wisdom-km/color-eink-work-badge/hardware/portrait/enclosure/output/portrait_native_C1_front.png

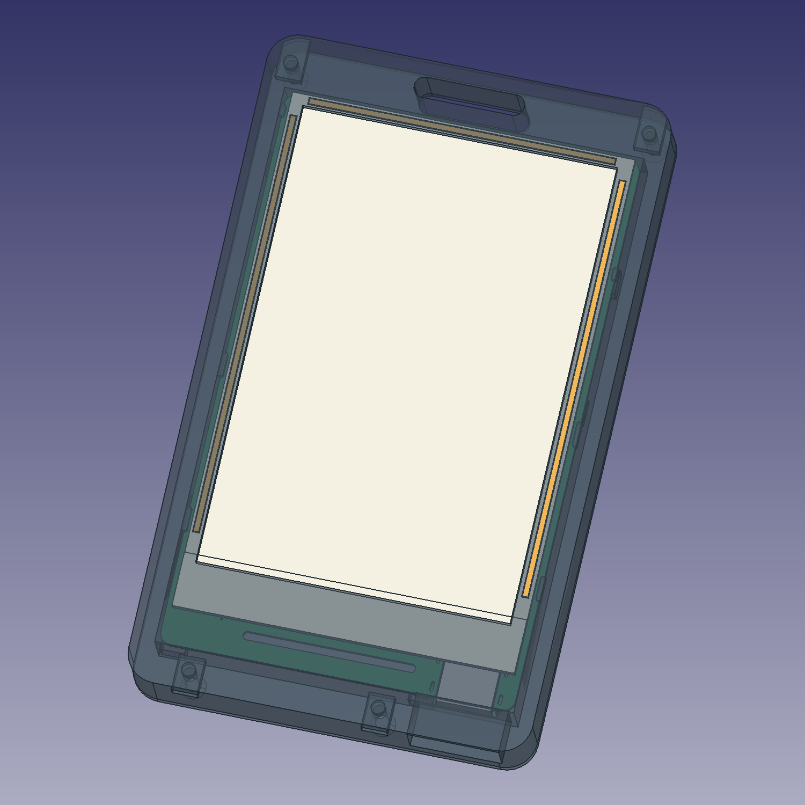
hardware/portrait/enclosure/output/portrait_native_C1_front.png
