wisdom-km/color-eink-work-badge/hardware/portrait/enclosure/output/pcb_back_layout_clipped.png

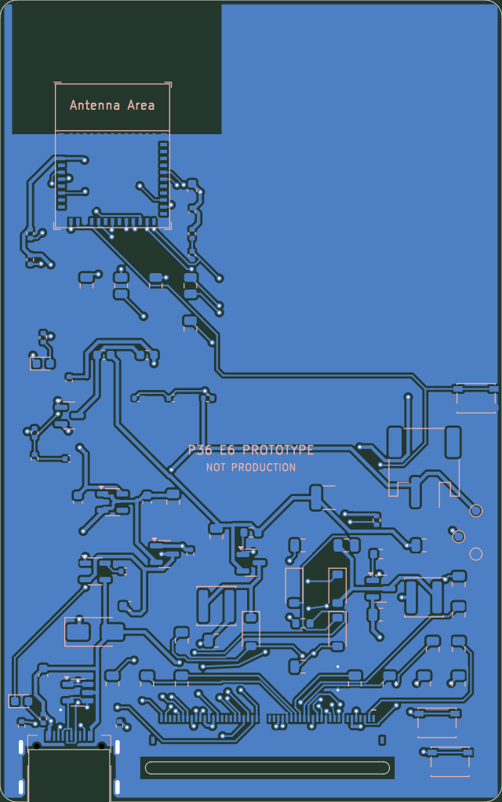
hardware/portrait/enclosure/output/pcb_back_layout_clipped.png
