wisdom-km/color-eink-work-badge/hardware/portrait/enclosure/output/portrait_actual_section.png

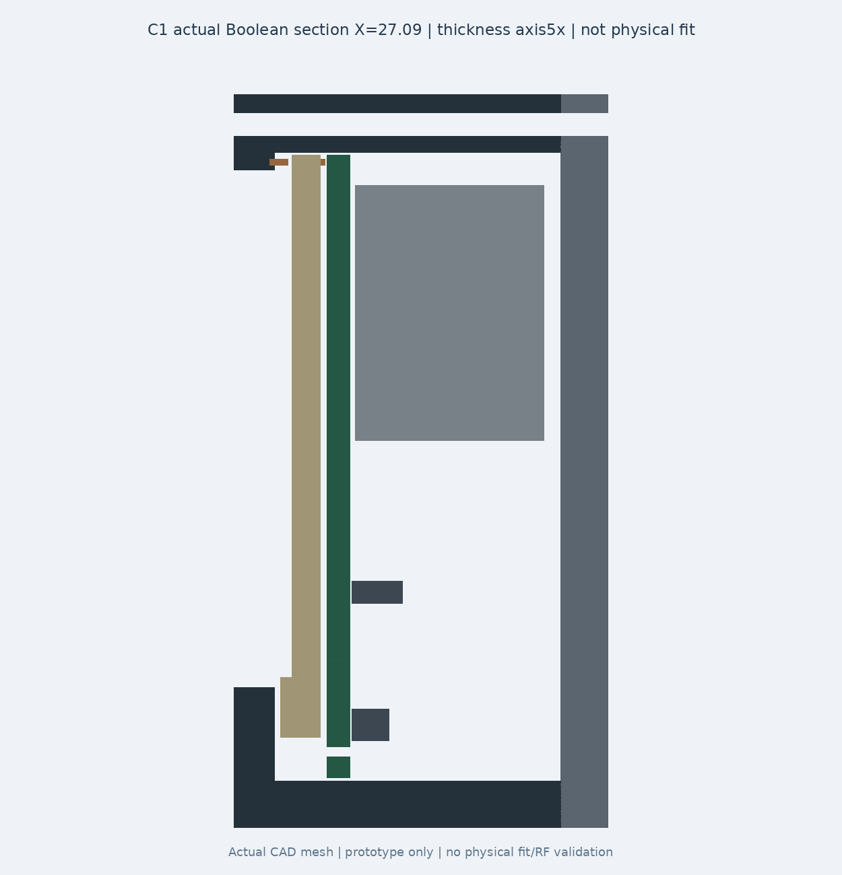
hardware/portrait/enclosure/output/portrait_actual_section.png
