wisdom-km/color-eink-work-badge/hardware/portrait/enclosure/output/portrait_exploded.png

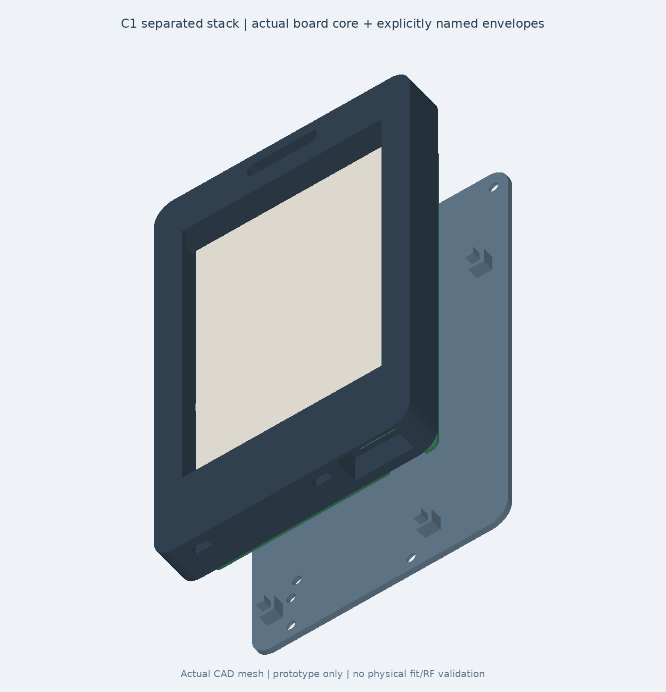
hardware/portrait/enclosure/output/portrait_exploded.png
