wisdom-km/color-eink-work-badge/hardware/portrait/enclosure/output/portrait_internal_envelopes.png

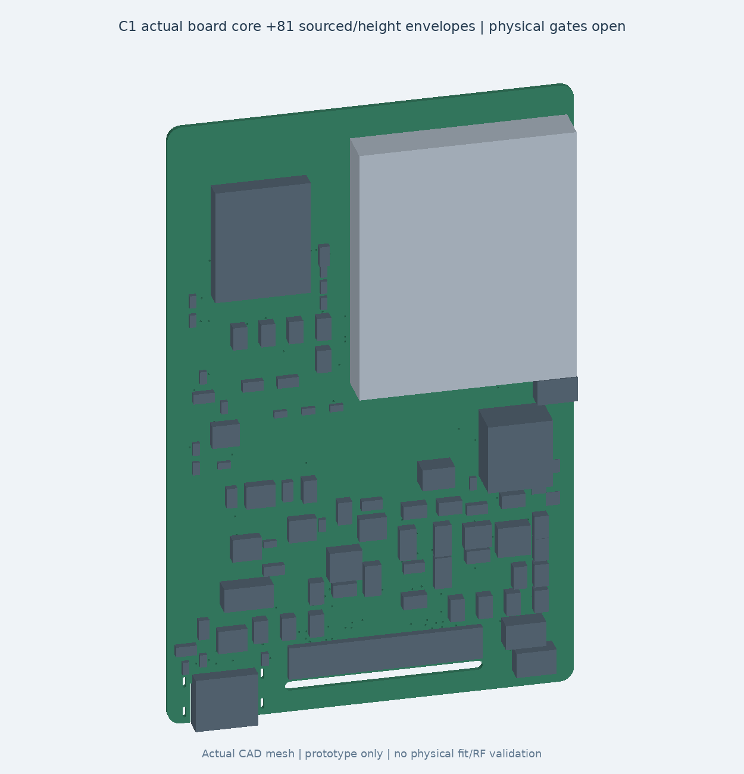
hardware/portrait/enclosure/output/portrait_internal_envelopes.png
