wisdom-km/color-eink-work-badge/hardware/portrait/enclosure/output/portrait_iso_front.png

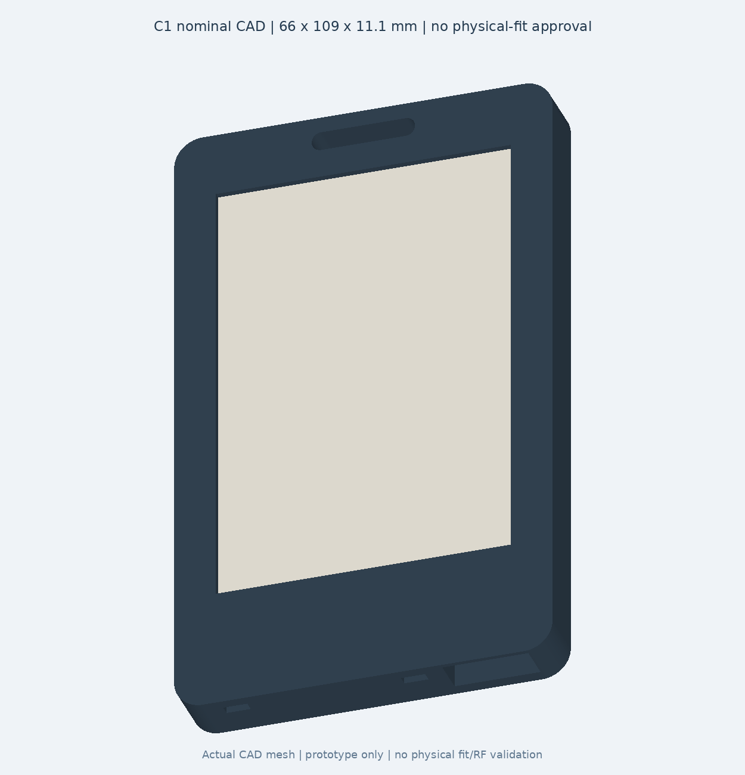
hardware/portrait/enclosure/output/portrait_iso_front.png
