wisdom-km/color-eink-work-badge/hardware/portrait/enclosure/output/portrait_layer_stack.png

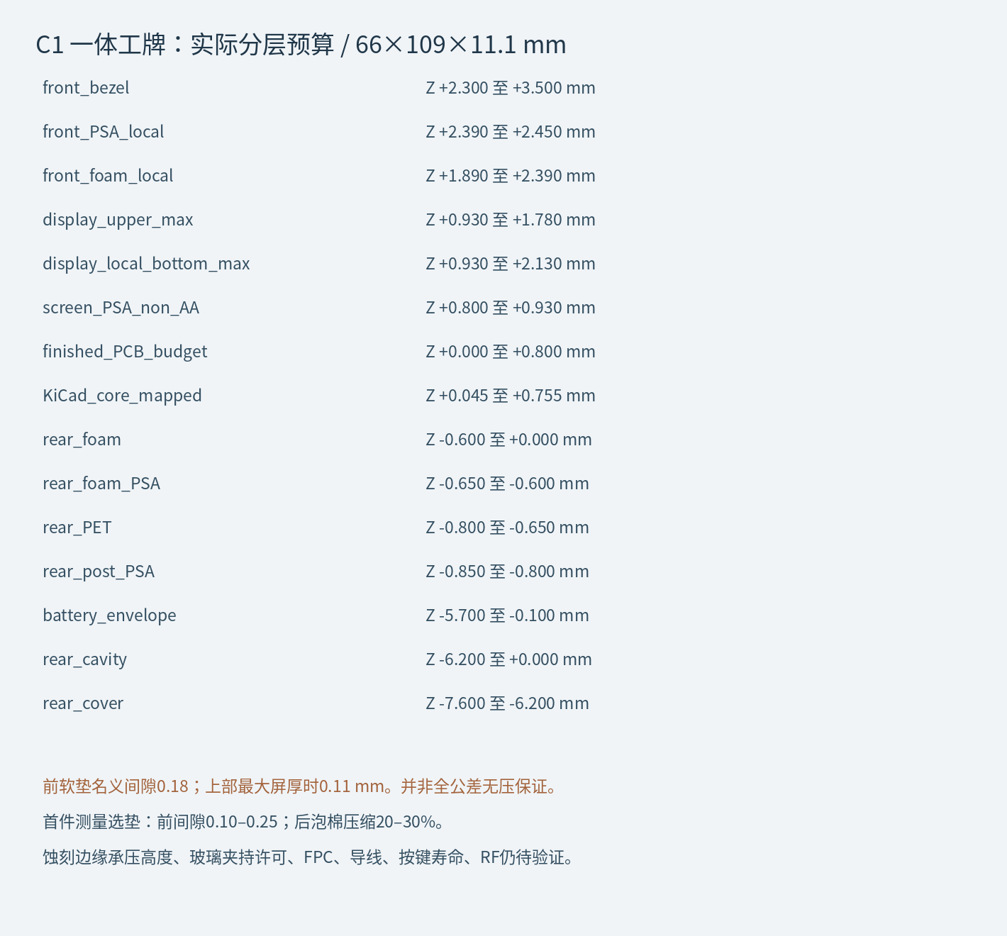
hardware/portrait/enclosure/output/portrait_layer_stack.png
