wisdom-km/color-eink-work-badge/hardware/portrait/enclosure/output/portrait_native_C1_internal.png

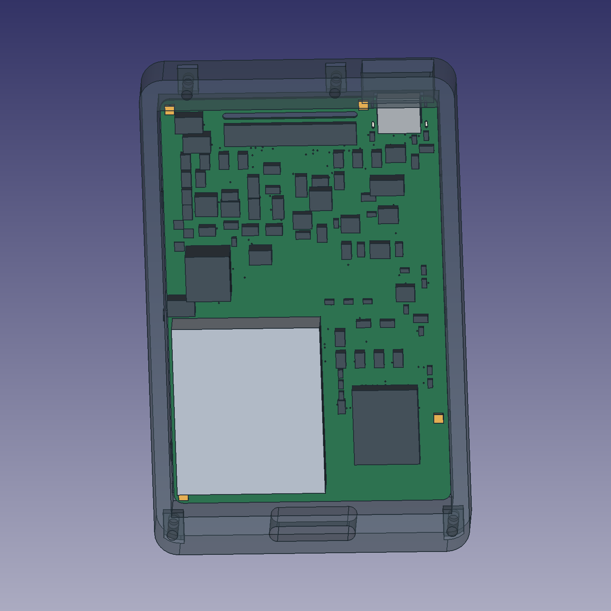
hardware/portrait/enclosure/output/portrait_native_C1_internal.png
