wisdom-km/color-eink-work-badge/hardware/portrait/enclosure/output/reference_ph_plug_keepout.step

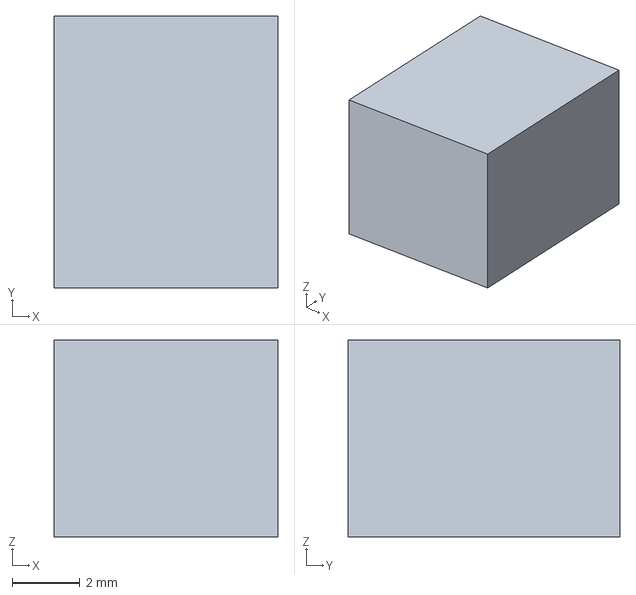
[picture p23: CAD file, 2026-09-30]
hardware/portrait/enclosure/output/reference_ph_plug_keepout.step
6.60 x 8.00 x 5.80 mm
