wisdom-km/color-eink-work-badge/hardware/portrait/enclosure/output/pcb_board_body.step

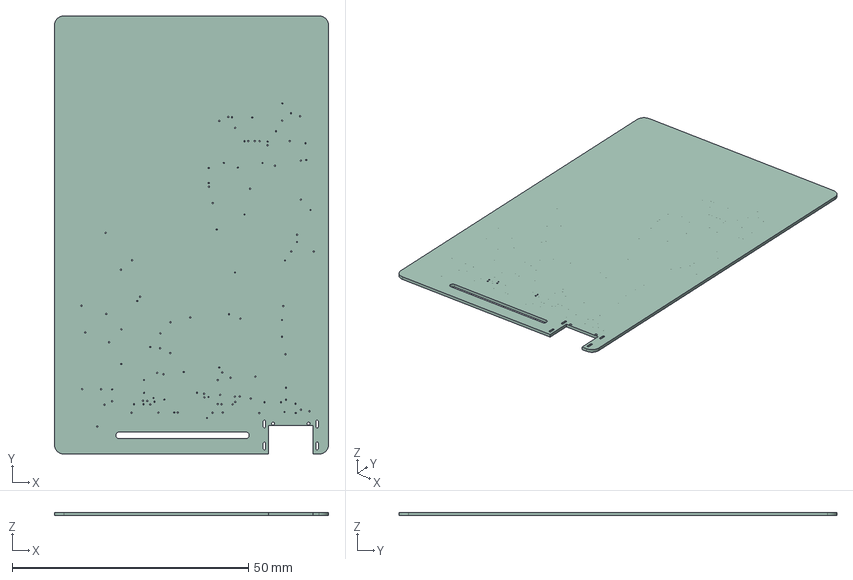
[picture p24: CAD file, 2026-09-30]
hardware/portrait/enclosure/output/pcb_board_body.step
58.0 x 92.6 x 0.71 mm
