wisdom-km/color-eink-work-badge/hardware/portrait/enclosure/output/reference_ScreenPSA_Right.step

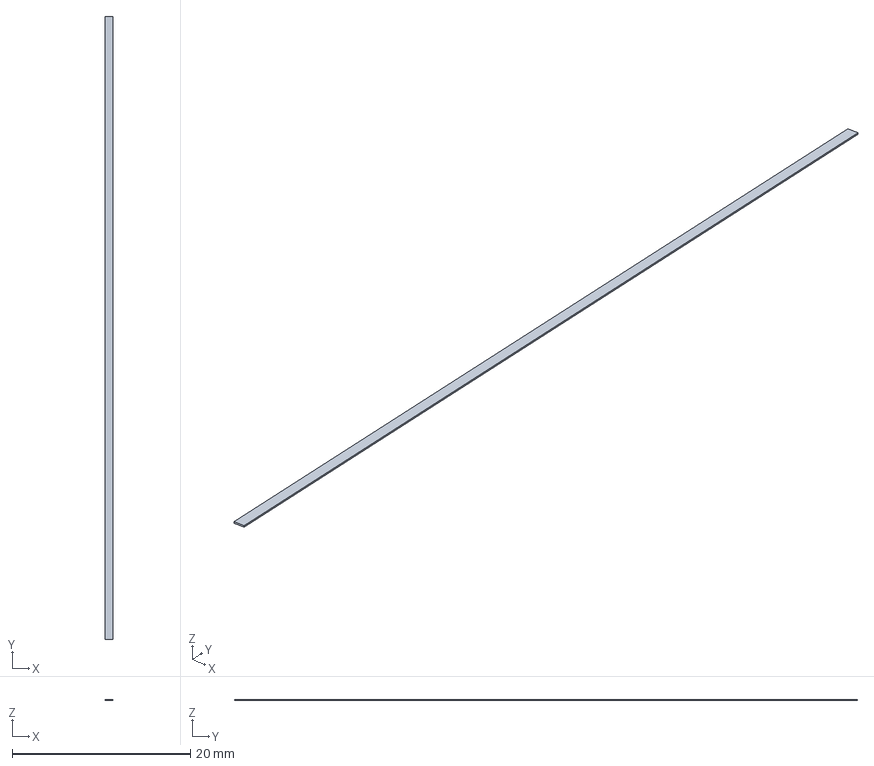
[picture p25: CAD file, 2026-09-30]
hardware/portrait/enclosure/output/reference_ScreenPSA_Right.step
0.9 x 70.0 x 0.13 mm
