wisdom-km/color-eink-work-badge/hardware/portrait/enclosure/output/reference_wire_keepout.step

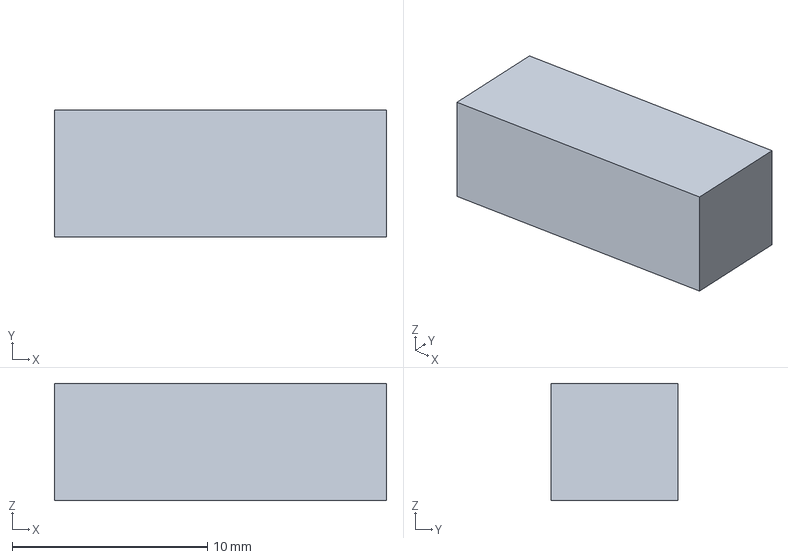
[picture p26: CAD file, 2026-09-30]
hardware/portrait/enclosure/output/reference_wire_keepout.step
17.0 x 6.50 x 6.00 mm
