wisdom-km/color-eink-work-badge/hardware/portrait/enclosure/output/reference_panel_global_audit.step

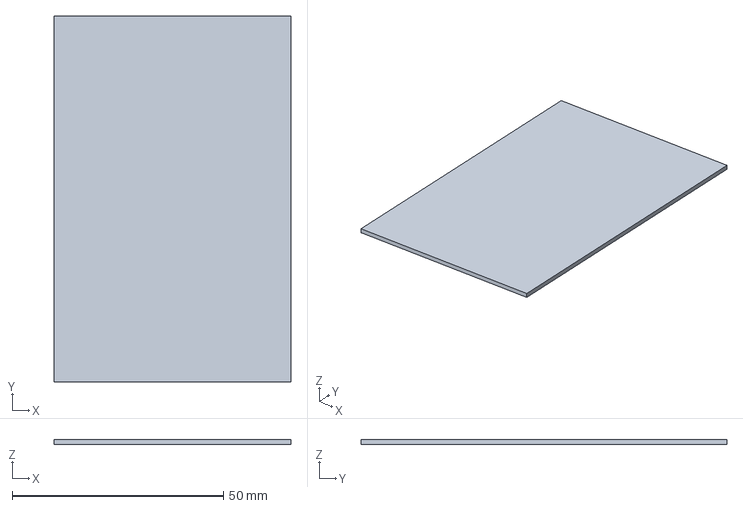
[picture p27: CAD file, 2026-09-30]
hardware/portrait/enclosure/output/reference_panel_global_audit.step
56.0 x 86.6 x 1.20 mm
