wisdom-km/color-eink-work-badge/hardware/portrait/enclosure/output/pcb_copper_audit.step

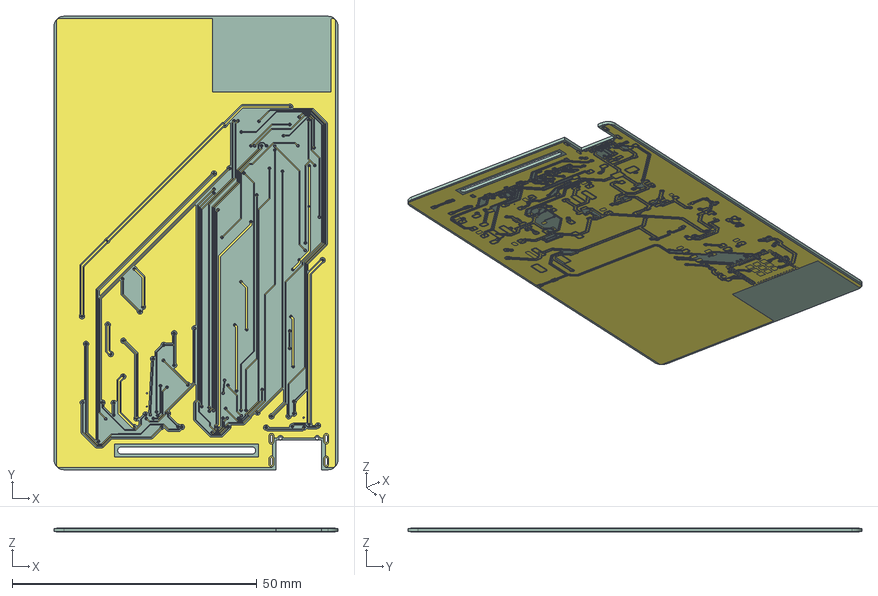
[picture p28: CAD file, 2026-09-30]
hardware/portrait/enclosure/output/pcb_copper_audit.step
58.0 x 92.6 x 0.78 mm
badge_copper
badge_pad
badge_via
badge_PCB
