wisdom-km/color-eink-work-badge/hardware/portrait/enclosure/output/reference_FrontFoam_Top.step

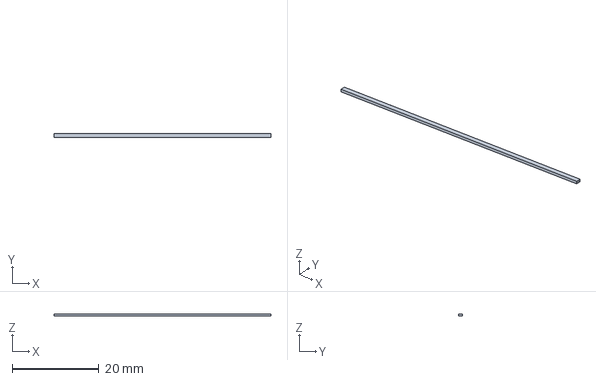
[picture p29: CAD file, 2026-09-30]
hardware/portrait/enclosure/output/reference_FrontFoam_Top.step
50.0 x 0.9 x 0.5 mm
