wisdom-km/color-eink-work-badge/hardware/portrait/enclosure/output/reference_usb_outline.step

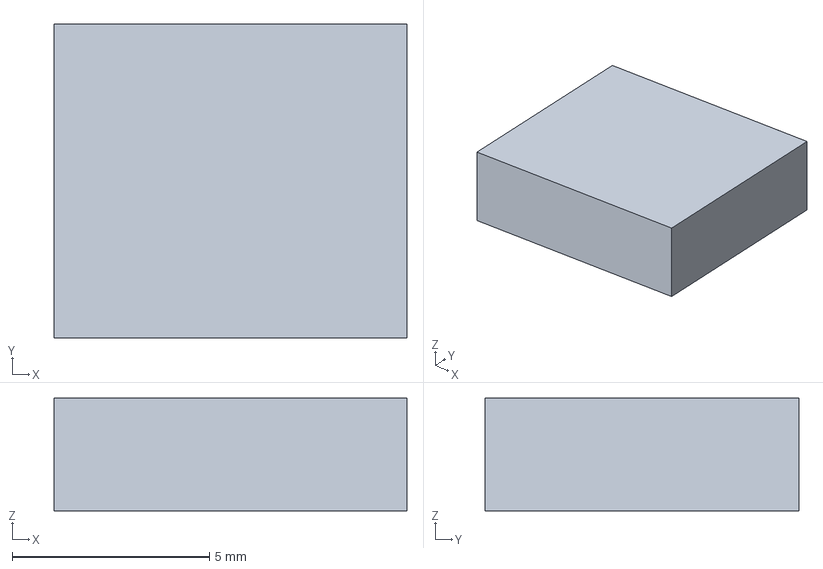
[picture p30: CAD file, 2026-09-30]
hardware/portrait/enclosure/output/reference_usb_outline.step
8.94 x 7.96 x 2.86 mm
