wisdom-km/color-eink-work-badge/hardware/portrait/enclosure/output/portrait_back_cover.step

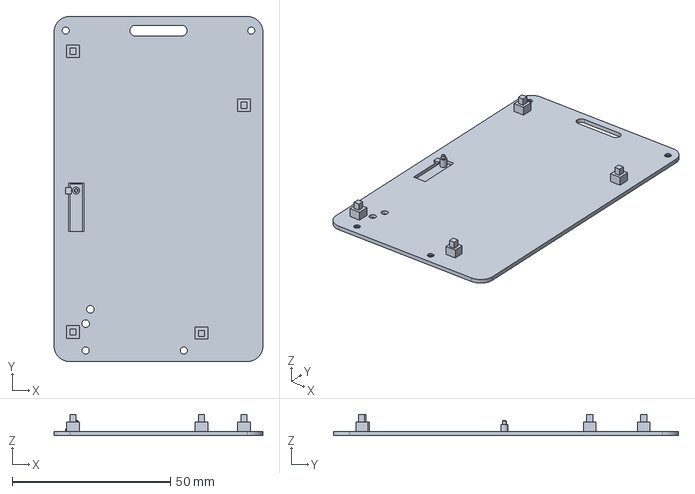
[picture p31: CAD file, 2026-09-30]
hardware/portrait/enclosure/output/portrait_back_cover.step
66.0 x 109.0 x 6.75 mm
