wisdom-km/color-eink-work-badge/hardware/portrait/enclosure/output/reference_FrontPSA_Top.step

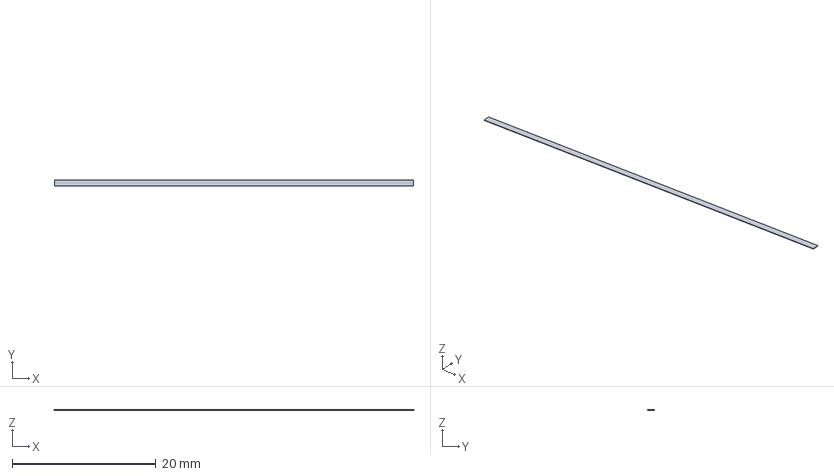
[picture p32: CAD file, 2026-09-30]
hardware/portrait/enclosure/output/reference_FrontPSA_Top.step
50.0 x 0.9 x 0.06 mm
