wisdom-km/color-eink-work-badge/hardware/portrait/enclosure/output/reference_ScreenPSA_Top.step

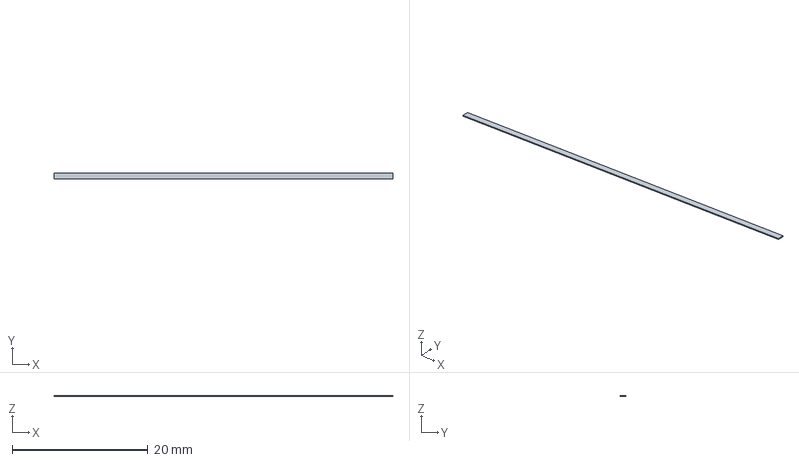
[picture p33: CAD file, 2026-09-30]
hardware/portrait/enclosure/output/reference_ScreenPSA_Top.step
50.0 x 0.9 x 0.13 mm
