wisdom-km/color-eink-work-badge/firmware/portrait36/src/shared_frame.cpp

// SPDX-License-Identifier: MIT
// Compile the same tested no-allocation implementation in this isolated target.
// Do not fork the validator or pull the historical H2 application into P1.
#include "../../src/portrait_frame.cpp"
