wisdom-km/color-eink-work-badge/tools/portrait_driver/vendor_oracle.h

// Generated from pinned official source, not the implementation under test.
#pragma once
const std::vector<Event> oracle_init = {{0,0xAA},{1,0x49},{1,0x55},{1,0x20},{1,0x08},{1,0x09},{1,0x18},{0,0x01},{1,0x3F},{0,0x00},{1,0x5F},{1,0x69},{0,0x05},{1,0x40},{1,0x1F},{1,0x1F},{1,0x2C},{0,0x08},{1,0x6F},{1,0x1F},{1,0x1F},{1,0x22},{0,0x06},{1,0x6F},{1,0x1F},{1,0x17},{1,0x17},{0,0x03},{1,0x00},{1,0x54},{1,0x00},{1,0x44},{0,0x60},{1,0x02},{1,0x00},{0,0x30},{1,0x08},{0,0x50},{1,0x3F},{0,0x61},{1,0x01},{1,0x90},{1,0x02},{1,0x58},{0,0xE3},{1,0x2F},{0,0x84},{1,0x01}};
const std::vector<Event> oracle_turn_on = {{0,0x04},{0,0x06},{1,0x6F},{1,0x1F},{1,0x16},{1,0x29},{0,0x12},{1,0x00},{0,0x02},{1,0x00}};
const std::vector<Event> oracle_sleep = {{0,0x07},{1,0xA5}};
